Br3nda/indoor-weather-station-v2/HouseSensor.h

#ifndef HOUSE_SENSOR_HEADER
#define HOUSE_SENSOR_HEADER

#include<WString.h> // For Arduino String class

struct APCredentials
{
    String ssid;
    String passphrase;
};


#endif // #ifndef HOUSE_SENSOR_HEADER
