Br3nda/indoor-weather-station-v2/DataUploader.cpp

#include "DataUploader.h"

#include <ESP8266HTTPClient.h>

#include <cassert>

/// Used for the static list of public APs that we know about at build time
/*!
 * The loginUrl is for public access points that require clicking an "I agree"
 * button to get access.
 */
struct StaticAPInfo
{
    char *ssid;
    char *passphrase;
    char *loginUrl;
};

#pragma GCC diagnostic push
// warning: deprecated conversion from string constant to 'char*'
#pragma GCC diagnostic ignored "-Wwrite-strings"
StaticAPInfo staticAPs[]{ {"Wicked Networks",  "", "http://google.com/"},
                          {"Library", "", ""} };
#pragma GCC diagnostic pop

// Units determined by length of delay in main loop()
#define DATAUPLOADER_WIFI_CONNECT_TIMEOUT 5000

DataUploader * DataUploader::instance(nullptr);

DataUploader::DataUploader( uint8_t *uploadData, size_t uploadLen,
                            APCredentials *preferredAP /* = nullptr */ ) :
    uploadDataPtr(uploadData),
    uploadDataLen(uploadLen)
{
    assert(instance == nullptr);
    instance = this;

    if( preferredAP ) {
        nextAPIndex = -1;
        requestedSSID = preferredAP->ssid;
        requestedPassphrase = preferredAP->passphrase;
    } else {
        nextAPIndex = 0;
    }

    WiFi.forceSleepWake();
    WiFi.enableSTA(true);

    // These don't seem to be setup properly...
    WiFi.onStationModeConnected(wifiConnectCb);
    WiFi.onStationModeDisconnected(wifiDisconnectCb);
    WiFi.onStationModeAuthModeChanged(wifiAuthChangedCb);
    WiFi.onStationModeGotIP(wifiGotIpCb);
    WiFi.onStationModeDHCPTimeout(wifiDhcpTimeoutCb);

    tryNextAp();
}


DataUploader::~DataUploader()
{
    WiFi.forceSleepBegin();

    assert(instance == this);
    instance = nullptr;
}


bool DataUploader::isDone()
{
    switch(state) {
        case DataUploaderState::TRYING_ACCESS_POINT:
        case DataUploaderState::WIFI_TBD:
            switch(WiFi.status()) {
                case WL_CONNECTED:
                    state = DataUploaderState::REGISTERING;
                    return false;

                case WL_NO_SSID_AVAIL:  // Requested SSID not seen
                case WL_CONNECT_FAILED: // Eg passphrase wrong
                case WL_CONNECTION_LOST:
                    Serial.println("Error connecting.");
                    state = DataUploaderState::TRYING_ACCESS_POINT;
                    tryNextAp();
                    return false;

                case WL_DISCONNECTED: // In this state while connecting
                    if( --connectCountdown == 0 ) {
                        Serial.println("Timed out while trying to connect...");
                        tryNextAp();
                        return false;
                    }
                default:
                    return false;
            }

        case DataUploaderState::REGISTERING:
            if( getLoginUrl() ) {
                HTTPClient c;
                c.begin( getLoginUrl() );
                Serial.print("Response code: ");
                Serial.println( c.GET() );
                for(size_t i(0); i < c.headers(); ++i)
                    Serial.println(c.header(i));
                Serial.println("Got:");
                Serial.println(c.getString());
                c.end();
            }
            state = DataUploaderState::UPLOADING;
            return false;

        case DataUploaderState::UPLOADING:
            if( doUpload() ) {
                state = DataUploaderState::SUCCEEDED;
                Serial.println("Uploaded successfully!");
                return true;
            } else {
                // TODO: Retry with this AP?
                state = DataUploaderState::TRYING_ACCESS_POINT;
                Serial.println("Upload failed.");
                tryNextAp();
                return false;
            }

        case DataUploaderState::SUCCEEDED:
        case DataUploaderState::CANT_CONNECT_TO_ANY:
            return true;

        default:
            assert(false);
            return false;
    }
}


bool DataUploader::succeeded() const
{
    return state == DataUploaderState::SUCCEEDED;
}


// Assumes state is TRYING_ACCESS_POINT on entry
void DataUploader::tryNextAp()
{
    if( nextAPIndex == -1 ) {
        Serial.print("Trying to connect to ");
        Serial.println(requestedSSID);
        WiFi.begin(requestedSSID.c_str(), requestedPassphrase.c_str());

        connectCountdown = DATAUPLOADER_WIFI_CONNECT_TIMEOUT;
        ++nextAPIndex;
    } else if( nextAPIndex < sizeof(staticAPs) / sizeof(staticAPs[0]) ) {
        Serial.print("Trying to connect to ");
        Serial.println(staticAPs[nextAPIndex].ssid);
        WiFi.begin( staticAPs[nextAPIndex].ssid,
                    staticAPs[nextAPIndex].passphrase );

        connectCountdown = DATAUPLOADER_WIFI_CONNECT_TIMEOUT;
        ++nextAPIndex;
    } else {
        Serial.println("Out of APs; failed");
        state = DataUploaderState::CANT_CONNECT_TO_ANY;
    }
}


const char * DataUploader::getLoginUrl() const
{
    auto apIndex(nextAPIndex - 1);

    if( apIndex == -1 || apIndex == sizeof(staticAPs) )
        return nullptr;

    if( strlen(staticAPs[apIndex].loginUrl) > 0)
        return staticAPs[apIndex].loginUrl;
    else
        return nullptr;
}


bool DataUploader::doUpload()
{
    HTTPClient client;
#if DATAUPLOADER_USE_HTTPS
  #error "This isn't implemented yet..."
#else
    if( !client.begin( DATAUPLOADER_SERVER_HOST,
                       DATAUPLOADER_SERVER_PORT,
                       DATAUPLOADER_SERVER_URI ) ) {
#endif // #if/else DATAUPLOADER_USE_HTTPS

        return false;
    }

    client.addHeader("Content-Type", "application/weatherdata");
    auto res( client.POST(uploadDataPtr, uploadDataLen) );

    client.end();

    return res == HTTP_CODE_OK ||
           res == HTTP_CODE_CREATED ||
           res == HTTP_CODE_ACCEPTED;
}


/*static*/ void DataUploader::wifiConnectCb(
        const WiFiEventStationModeConnected &eventInfo )
{
    instance->state = DataUploaderState::WIFI_TBD;
    Serial.println("TEST - WiFi connected");
}


/*static*/ void DataUploader::wifiDisconnectCb(
        const WiFiEventStationModeDisconnected &eventInfo )
{
    instance->state = DataUploaderState::WIFI_TBD;
    Serial.println("TEST - WiFi disconnected");
}


/*static*/ void DataUploader::wifiAuthChangedCb(
        const WiFiEventStationModeAuthModeChanged &eventInfo )
{
    instance->state = DataUploaderState::WIFI_TBD;
    Serial.println("TEST - WiFi auth mode changed");
}


/*static*/ void DataUploader::wifiGotIpCb(
        const WiFiEventStationModeGotIP &eventInfo)
{
    instance->state = DataUploaderState::WIFI_TBD;
    Serial.println("TEST - WiFi got IP");
}


/*static*/ void DataUploader::wifiDhcpTimeoutCb(void)
{
    instance->state = DataUploaderState::WIFI_TBD;
    Serial.println("TEST - WiFi DHCP timeout");
}
