Br3nda/indoor-weather-station-v2/PC8563.cpp

/*   
 *   Copyright (C) 2016 Paul Campbell

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
 *   You should have received a copy of the GNU General Public License
 *   along with this program.  If not, see <http://www.gnu.org/licenses/>.
 */

#include <Wire.h>

#include "PC8563.h"

#define ADDRESS 0x51 

PC8563::PC8563()
{
  Wire.begin();
}
  
bool
PC8563::begin()
{
  Wire.beginTransmission((uint8_t)ADDRESS);
  Wire.write((uint8_t)0);
  Wire.endTransmission();

  Wire.requestFrom((uint8_t)ADDRESS, (uint8_t)1);
  if (!Wire.available()) 
	  return false;
  return true;
}

bool
PC8563::read(pc_time &tm)
{
  Wire.beginTransmission((uint8_t)ADDRESS);
  Wire.write((uint8_t)2);
  Wire.endTransmission();
  Wire.requestFrom((uint8_t)ADDRESS, (uint8_t)7);	
  if (!Wire.available())
	  return false;
  int v = Wire.read();
  if (v&0x80)
	  return false;
  tm.second= (v&0xf) + (10*((v>>4)&0x7));
  v = Wire.read();
  tm.minute = (v&0xf) + (10*((v>>4)&0x7));
  v = Wire.read();
  tm.hour = (v&0xf) + (10*((v>>4)&0x3));
  v = Wire.read();
  tm.day = (v&0xf) + (10*((v>>4)&0x3));
  v = Wire.read();
  v = Wire.read();
  tm.month = (v&0xf) + (10*((v>>4)&0x1));
  tm.year = (v&0x80?2100:2000);
  v = Wire.read();
  tm.year += (v&0xf) + (10*((v>>4)&0xf));
  return true;
}
  
bool
PC8563::write(pc_time &tm)
{
  Wire.beginTransmission((uint8_t)ADDRESS);
  Wire.write((uint8_t)0);
  Wire.write((uint8_t)0x20);	// stop
  Wire.write((uint8_t)0x00);	// no alarm
  Wire.write((uint8_t)((tm.second%10)|((tm.second/10)<<4)));
  Wire.write((uint8_t)((tm.minute%10)|((tm.minute/10)<<4)));
  Wire.write((uint8_t)((tm.hour%10)|((tm.hour/10)<<4)));
  Wire.write((uint8_t)((tm.day%10)|((tm.day/10)<<4)));
  Wire.write((uint8_t)1); // don't care
  Wire.write((uint8_t)((tm.month%10)|((tm.month/10)<<4)|(tm.year>=2100?0x80:0)));
  int v = tm.year-2000;
  if (v >= 100)
	  v -= 100;
  Wire.write((uint8_t)((v%10)|((v/10)<<4)));
  Wire.endTransmission();
  Wire.beginTransmission((uint8_t)ADDRESS);
  Wire.write((uint8_t)0);
  Wire.write((uint8_t)0); // start
  Wire.endTransmission();
  return true;
}
PC8563 PC8563_RTC;
