Br3nda/indoor-weather-station-v2/HTS221.h

/*
 * HTS221.h
 *
 * Created: 02/01/2015 20:50:30
 *  Author: smkk
 */


#ifndef HTS221_H_
#define HTS221_H_

#include <Arduino.h>


class HTS221
{
public:
    HTS221(void);
    bool begin(void);
    bool activate(void);
    bool deactivate(void);

    bool bduActivate(void);
    bool bduDeactivate(void);

    const int readHumidity(void);
    const double readTemperature(void);
    bool storeCalibration(void);
    unsigned char _h0_rH, _h1_rH;
    unsigned int  _T0_degC, _T1_degC;
    unsigned int  _H0_T0, _H1_T0;
    unsigned int  _T0_OUT, _T1_OUT;
private:
    double _temperature;
    int _humidity;
    uint8_t _address;

    byte readRegister(byte slaveAddress, byte regToRead);
    bool writeRegister(byte slaveAddress, byte regToWrite, byte dataToWrite);
};


extern HTS221 smeHumidity;


#endif /* HTS221_H_ */
